ktane-irl/ktane-irl/modules/01-clockModule/CM01-circuit/CM-01_circuit.kicad_sch

## KiCad design modules/01-clockModule/CM01-circuit/CM-01_circuit.kicad_sch (2023-03-28)

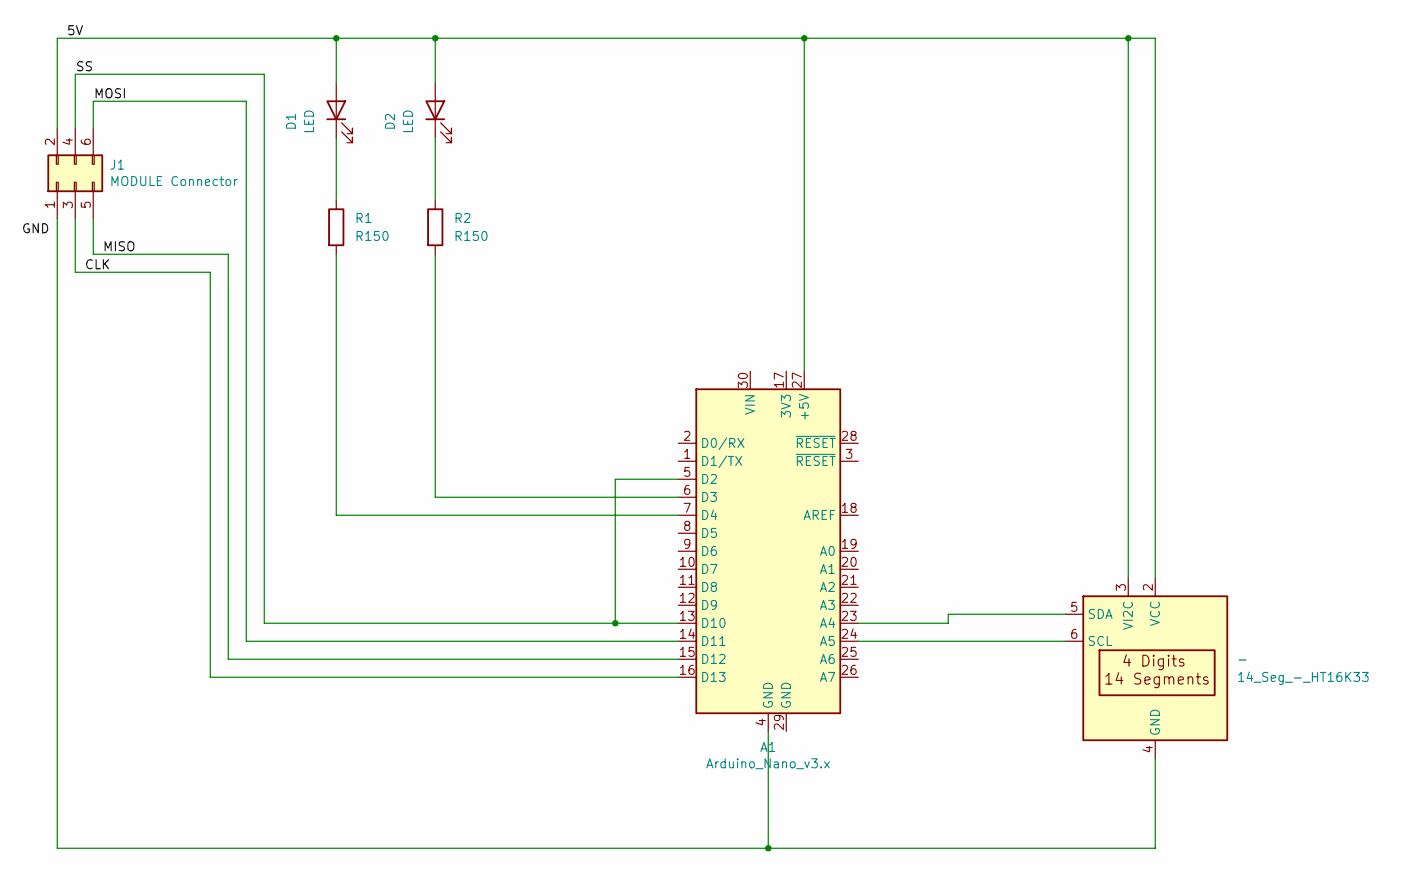
[picture p16: schematic CM-01_circuit.kicad_sch]

Parts:
-: 14_Seg_-_HT16K33
A1: Arduino_Nano_v3.x; Arduino_Nano
D1, D2: LED
J1: MODULE Connector
R1, R2: R150

Connections:
5V: -.2 (VCC), -.3 (VI2C), A1.27 (+5V), D1.2 (A), D2.2 (A), J1.2
CLK: A1.16 (D13), J1.3
MISO: A1.15 (D12), J1.5
MOSI: A1.14 (D11), J1.6
unnamed: -.4 (GND), A1.4 (GND), J1.1
unnamed: -.5 (SDA), A1.23 (A4)
unnamed: -.6 (SCL), A1.24 (A5)
unnamed: A1.6 (D3), R2.2
unnamed: A1.7 (D4), R1.2
unnamed: D1.1 (K), R1.1
unnamed: D2.1 (K), R2.1
SS: A1.5 (D2), A1.13 (D10), J1.4
