ktane-irl/ktane-irl/modules/00-case/CA01-circuit/case_module.kicad_sch

## KiCad design modules/00-case/CA01-circuit/case_module.kicad_sch (2023-03-21)

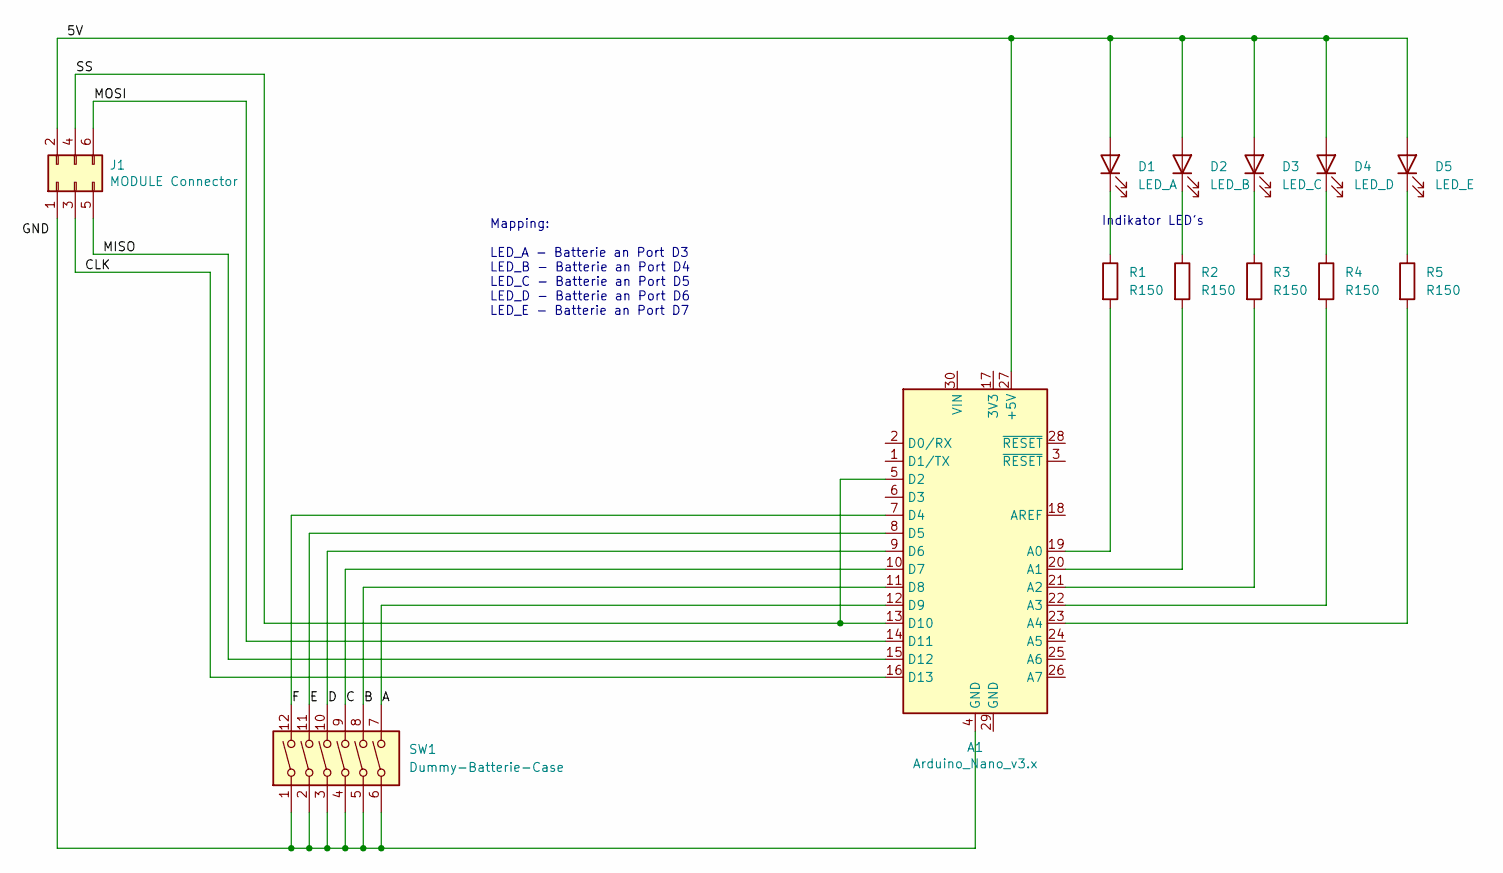
[picture p18: schematic case_module.kicad_sch]

Parts:
A1: Arduino_Nano_v3.x; Arduino_Nano
D1: LED_A
D2: LED_B
D3: LED_C
D4: LED_D
D5: LED_E
J1: MODULE Connector
R1, R2, R3, R4, R5: R150
SW1: Dummy-Batterie-Case

Connections:
5V: A1.27 (+5V), D1.2 (A), D2.2 (A), D3.2 (A), D4.2 (A), D5.2 (A), J1.2
A: A1.12 (D9), SW1.7
B: A1.11 (D8), SW1.8
C: A1.10 (D7), SW1.9
CLK: A1.16 (D13), J1.3
D: A1.9 (D6), SW1.10
E: A1.8 (D5), SW1.11
F: A1.7 (D4), SW1.12
MISO: A1.15 (D12), J1.5
MOSI: A1.14 (D11), J1.6
unnamed: A1.4 (GND), J1.1, SW1.1, SW1.2, SW1.3, SW1.4, SW1.5, SW1.6
unnamed: A1.19 (A0), R1.2
unnamed: A1.20 (A1), R2.2
unnamed: A1.21 (A2), R3.2
unnamed: A1.22 (A3), R4.2
unnamed: A1.23 (A4), R5.2
unnamed: D1.1 (K), R1.1
unnamed: D2.1 (K), R2.1
unnamed: D3.1 (K), R3.1
unnamed: D4.1 (K), R4.1
unnamed: D5.1 (K), R5.1
SS: A1.5 (D2), A1.13 (D10), J1.4

Notes on the sheet:
Indikator LED's
Mapping: LED_A - Batterie an Port D3 LED_B - Batterie an Port D4 LED_C - Batterie an Port D5 LED_D - Batterie an Port D6 LED_E - Batterie an Port D7
