ktane-irl/ktane-irl/modules/02-wires/WI01-circuit/wires.kicad_sch

## KiCad design modules/02-wires/WI01-circuit/wires.kicad_sch (2023-03-21)

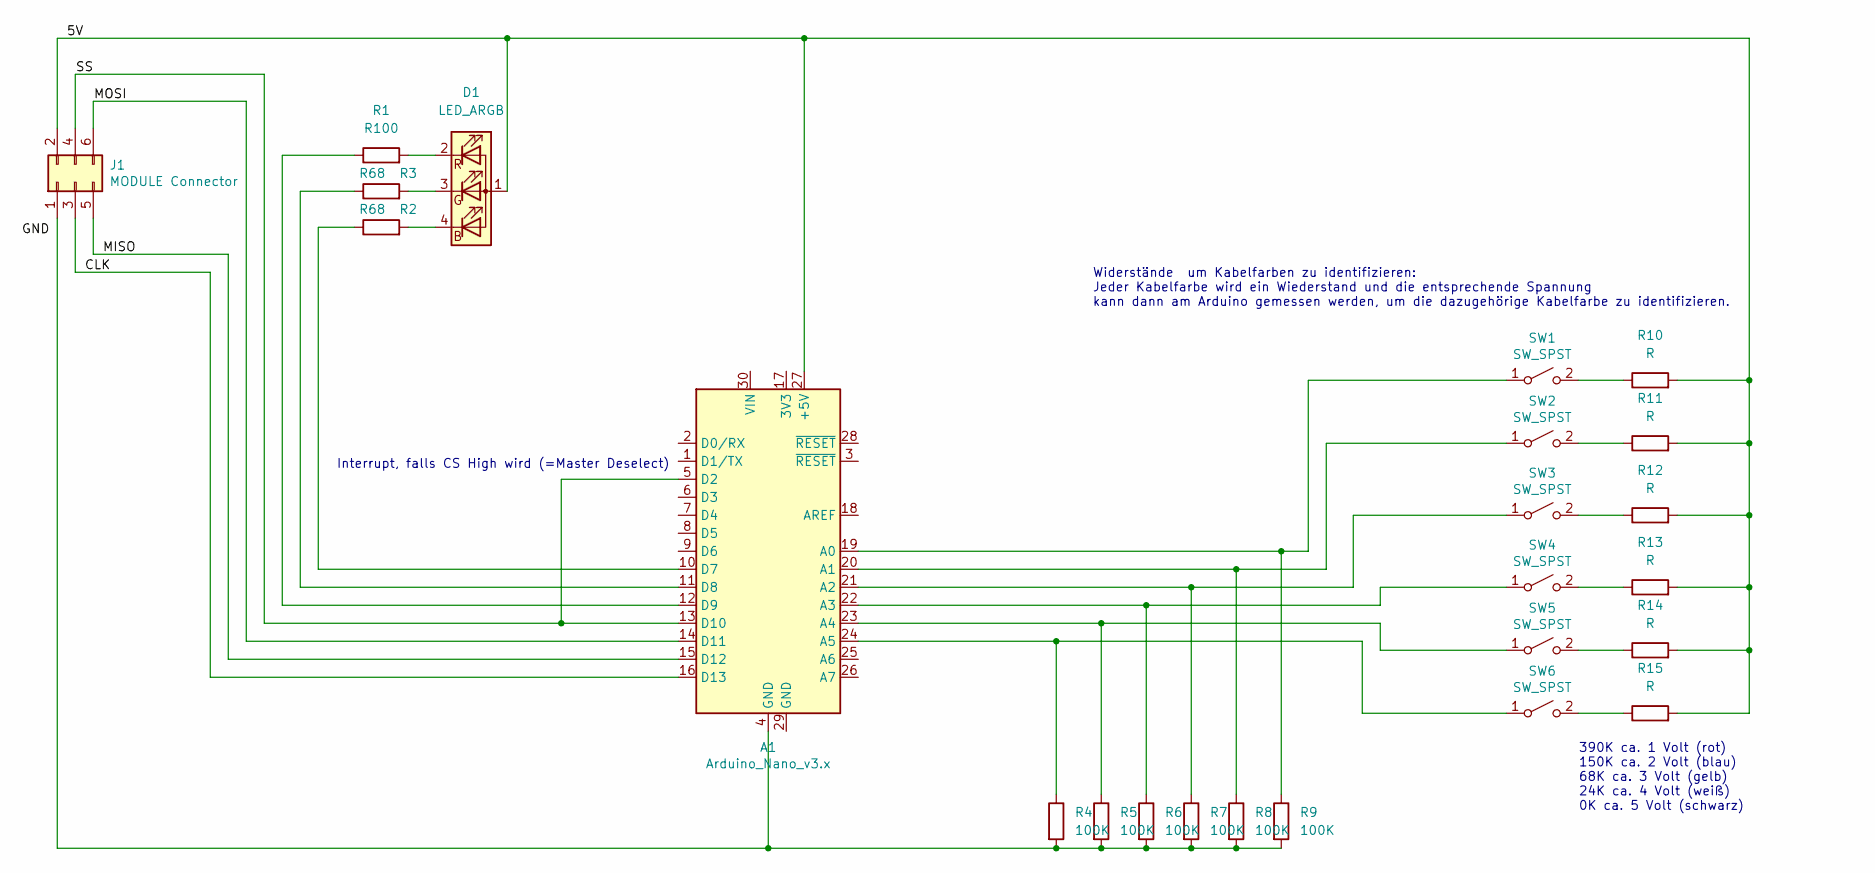
[picture p19: schematic wires.kicad_sch]

Parts:
A1: Arduino_Nano_v3.x; Arduino_Nano
D1: LED_ARGB
J1: MODULE Connector
R1: R100
R2, R3: R68
R4, R5, R6, R7, R8, R9: 100K
R10, R11, R12, R13, R14, R15: R
SW1, SW2, SW3, SW4, SW5, SW6: SW_SPST

Connections:
5V: A1.27 (+5V), D1.1 (A), J1.2, R10.2, R11.2, R12.2, R13.2, R14.2, R15.2
CLK: A1.16 (D13), J1.3
MISO: A1.15 (D12), J1.5
MOSI: A1.14 (D11), J1.6
unnamed: A1.4 (GND), J1.1, R4.2, R5.2, R6.2, R7.2, R8.2, R9.2
unnamed: A1.10 (D7), R3.1
unnamed: A1.11 (D8), R2.1
unnamed: A1.12 (D9), R1.1
unnamed: A1.19 (A0), R9.1, SW1.1 (A)
unnamed: A1.20 (A1), R8.1, SW2.1 (A)
unnamed: A1.21 (A2), R7.1, SW3.1 (A)
unnamed: A1.22 (A3), R6.1, SW4.1 (A)
unnamed: A1.23 (A4), R5.1, SW5.1 (A)
unnamed: A1.24 (A5), R4.1, SW6.1 (A)
unnamed: D1.2 (RK), R1.2
unnamed: D1.3 (GK), R2.2
unnamed: D1.4 (BK), R3.2
unnamed: R10.1, SW1.2 (B)
unnamed: R11.1, SW2.2 (B)
unnamed: R12.1, SW3.2 (B)
unnamed: R13.1, SW4.2 (B)
unnamed: R14.1, SW5.2 (B)
unnamed: R15.1, SW6.2 (B)
SS: A1.5 (D2), A1.13 (D10), J1.4

Notes on the sheet:
390K ca. 1 Volt (rot) 150K ca. 2 Volt (blau) 68K ca. 3 Volt (gelb) 24K ca. 4 Volt (weiß) 0K ca. 5 Volt (schwarz)
Interrupt, falls CS High wird (=Master Deselect)
Widerstände um Kabelfarben zu identifizieren: Jeder Kabelfarbe wird ein Wiederstand und die entsprechende Spannung kann dann am Arduino gemessen werden, um die dazugehörige Kabelfarbe zu identifizieren.
