ktane-irl/ktane-irl/modules/11-mazes/MA01-circuit/maze.kicad_sch

## KiCad design modules/11-mazes/MA01-circuit/maze.kicad_sch (2023-03-21)

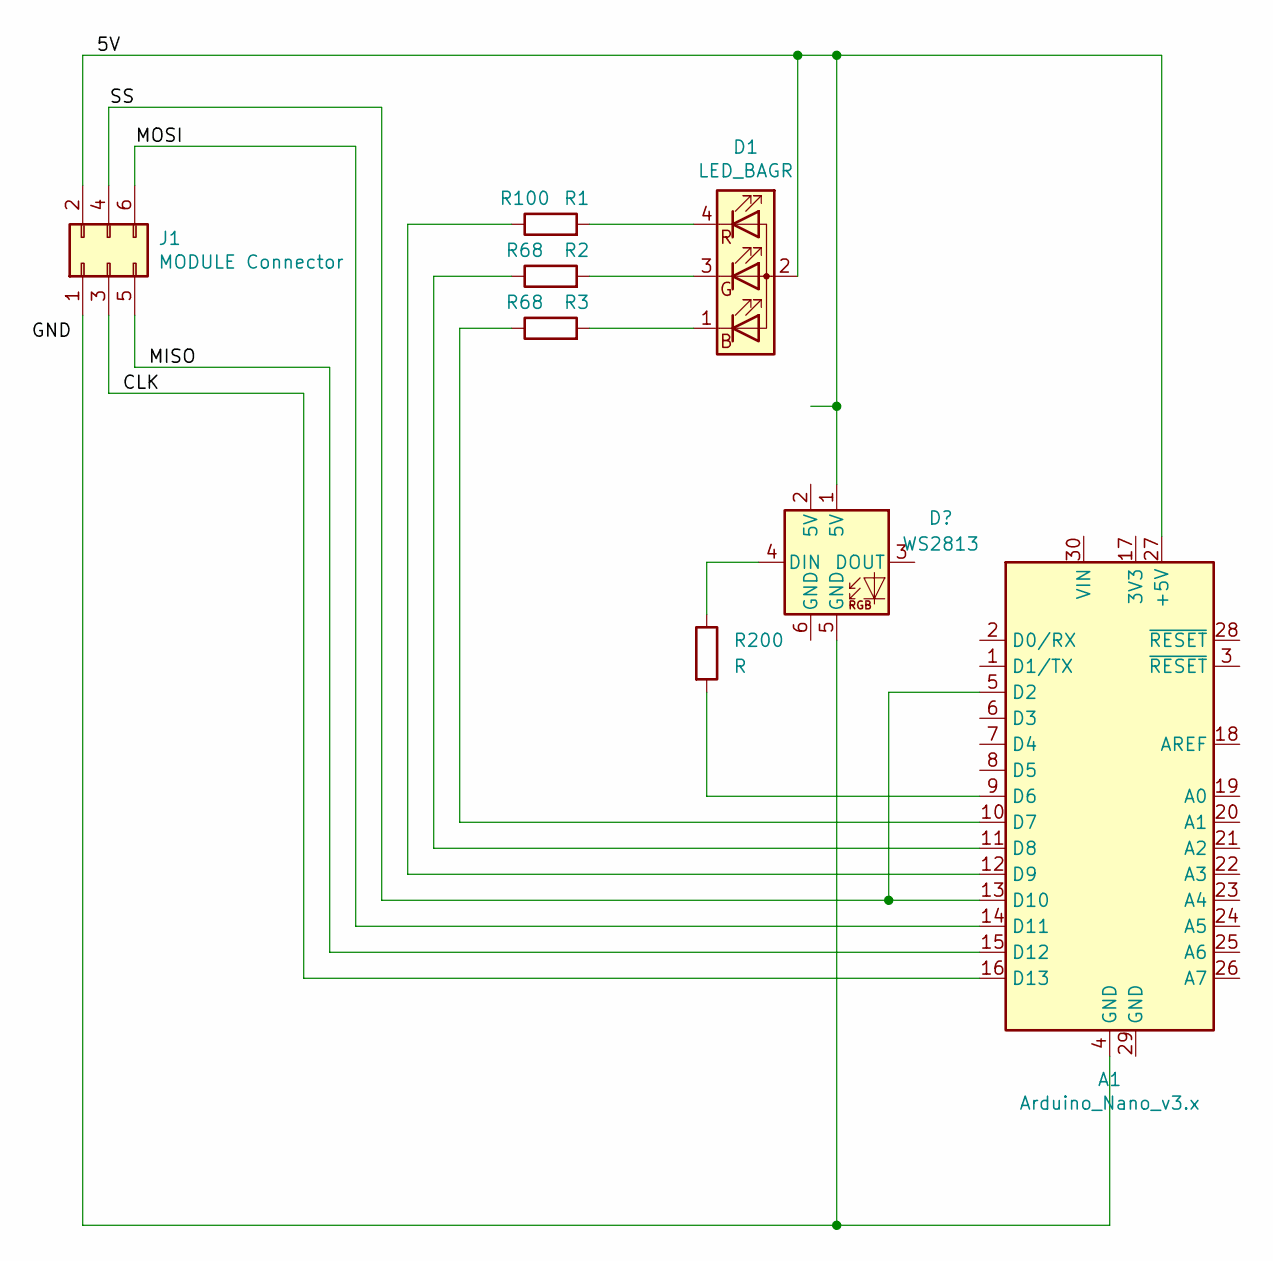
[picture p20: schematic maze.kicad_sch]

Parts:
A1: Arduino_Nano_v3.x; Arduino_Nano
D1: LED_BAGR
J1: MODULE Connector
R1: R100
R2, R3: R68
R200: R

Connections:
5V: A1.27 (+5V), D1.2 (A), J1.2
CLK: A1.16 (D13), J1.3
MISO: A1.15 (D12), J1.5
MOSI: A1.14 (D11), J1.6
unnamed: A1.4 (GND), J1.1
unnamed: A1.9 (D6), R200.2
unnamed: A1.10 (D7), R3.1
unnamed: A1.11 (D8), R2.1
unnamed: A1.12 (D9), R1.1
unnamed: D1.1 (BK), R3.2
unnamed: D1.3 (GK), R2.2
unnamed: D1.4 (RK), R1.2
SS: A1.5 (D2), A1.13 (D10), J1.4
